amberlab-eclettica/car-ogna/img/PXL_20241027_181953164.jpg

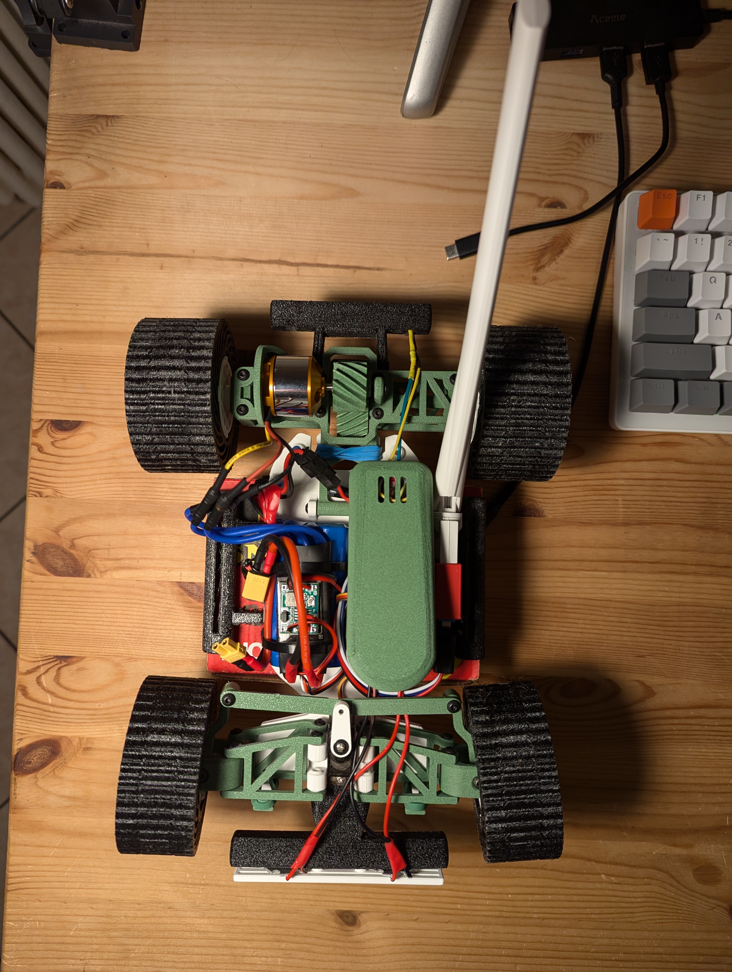
img/PXL_20241027_181953164.jpg
