amberlab-eclettica/car-ogna/img/PXL_20241027_182005586.jpg

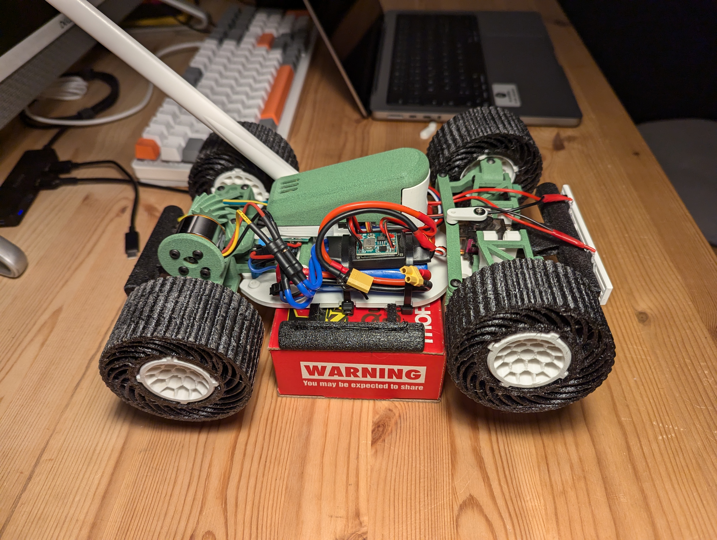
img/PXL_20241027_182005586.jpg
